richard42/ESP32FloppyTester/ESP32_FloppyTester/CodecGCR.cpp

//////////////////////////////////////////////////////////////////////////
// ESP32_FloppyTester
// CodecGCR.cpp
// 
// Copyright (C) 2024  Richard Goedeken
//
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
#include <stdint.h>
#include <stdlib.h>
#include <math.h>

#include <Arduino.h>

#include <map>

#include "FloppyTester.h"
#include "CodecGCR.h"

#define DELTA_ITEM(X) m_pusDeltaBuffers[(X)>>12][(X)&0x0fff]

//////////////////////////////////////////////////////////////////////////
// constructor and destructor

DecoderGCR::DecoderGCR(const uint16_t *pusDeltaBuffers[], uint32_t uiDeltaMax)
 : m_pusDeltaBuffers(pusDeltaBuffers)
 , m_uiDeltaMax(uiDeltaMax)
 , m_uiSectorDataLength(0)
{
}

DecoderGCR::~DecoderGCR()
{
}

//////////////////////////////////////////////////////////////////////////
// accessors

//////////////////////////////////////////////////////////////////////////
// static methods

bool DecoderGCR::DetectEncoding(const uint32_t auiCountByWavelen[16], const float afAverageByWavelen[16],
                                uint16_t *m_pusDeltaBuffers[], uint32_t uiDeltaMax, float fPeakCenters[3])
{
    // go through the histogram and find isolated peaks in the histogram
    uint32_t uiPeakIdx[4];
    uint32_t uiNumPeaks = 0;
    const uint32_t uiThreshold = uiDeltaMax / 30;
    const uint32_t uiLowThresh = uiDeltaMax / 250;
    bool bAboveThresh = false;
    for (uint32_t uiIdx = 0; uiIdx < 16; uiIdx++)
    {
        if (auiCountByWavelen[uiIdx] > uiThreshold)
        {
            if (bAboveThresh == false)
            {
                bAboveThresh = true;
                uiPeakIdx[uiNumPeaks] = uiIdx;
            }
            else
            {
                if (auiCountByWavelen[uiIdx] > auiCountByWavelen[uiPeakIdx[uiNumPeaks]])
                {
                    uiPeakIdx[uiNumPeaks] = uiIdx;
                }
            }
        }
        else
        {
            if (bAboveThresh == true)
            {
                bAboveThresh = false;
                uiNumPeaks++;
            }
        }
        if (uiNumPeaks == 4)
            break;
    }
    if (bAboveThresh == true)
        uiNumPeaks++;

    // special hack for test tracks written with all zeros -- they have a very small 3x signal
    if (uiNumPeaks == 2 && afAverageByWavelen[uiPeakIdx[0]] >= 3.0 && afAverageByWavelen[uiPeakIdx[0]] <= 4.2 &&
                           afAverageByWavelen[uiPeakIdx[1]] >= 6.1 && afAverageByWavelen[uiPeakIdx[1]] <= 8.2 &&
        (auiCountByWavelen[3] + auiCountByWavelen[4] + auiCountByWavelen[6] + auiCountByWavelen[7] + auiCountByWavelen[8]) > uiDeltaMax * 0.96)
    {
        uint32_t uiCount3x = 0, uiMaxIdx = 0;
        for (uint32_t ui = 9; ui <= 12; ui++)
        {
            const uint32_t uiThisCount = auiCountByWavelen[ui];
            uiCount3x += uiThisCount;
            if (ui == 9 || uiThisCount > auiCountByWavelen[uiMaxIdx])
            {
                uiMaxIdx = ui;
            }
        }
        if (uiCount3x > uiLowThresh)
        {
            uiPeakIdx[2] = uiMaxIdx;
            uiNumPeaks = 3;
        }
    }

    // and another special hack for test tracks written with all ones -- they have a small 2x signal
    if (uiNumPeaks == 2 && afAverageByWavelen[uiPeakIdx[0]] >= 3.0 && afAverageByWavelen[uiPeakIdx[0]] <= 4.2 &&
                           afAverageByWavelen[uiPeakIdx[1]] >= 9.2 && afAverageByWavelen[uiPeakIdx[1]] <= 12.2 &&
        (auiCountByWavelen[3] + auiCountByWavelen[4] + auiCountByWavelen[9] + auiCountByWavelen[10] + auiCountByWavelen[11] + auiCountByWavelen[12]) > uiDeltaMax * 0.94)
    {
        uint32_t uiCount2x = 0, uiMaxIdx = 0;
        for (uint32_t ui = 6; ui <= 8; ui++)
        {
            const uint32_t uiThisCount = auiCountByWavelen[ui];
            uiCount2x += uiThisCount;
            if (ui == 6 || uiThisCount > auiCountByWavelen[uiMaxIdx])
            {
                uiMaxIdx = ui;
            }
        }
        if (uiCount2x > uiLowThresh)
        {
            uiPeakIdx[2] = uiPeakIdx[1];
            uiPeakIdx[1] = uiMaxIdx;
            uiNumPeaks = 3;
        }
    }

    // if this track is GCR encoded, we expect to see 3 peaks, at 1x, 2x, and 3x of the base wavelength
    if (uiNumPeaks != 3)
        return false;

    fPeakCenters[0] = afAverageByWavelen[uiPeakIdx[0]];
    fPeakCenters[1] = afAverageByWavelen[uiPeakIdx[1]];
    fPeakCenters[2] = afAverageByWavelen[uiPeakIdx[2]];

    // use an iterative algorithm to converge on the true centers of each histogram peak
    for (uint32_t uiLoopIter = 0; uiLoopIter < 20; uiLoopIter++)
    {
        // calculate the average position of each delta value within +/- 0.5 microseconds of each peak
        float fNewPeakSums[3] = {0, 0, 0};
        uint32_t uiNewPeakCnts[3] = {0, 0, 0};
        for (uint32_t ui = 0; ui < uiDeltaMax; ui++)
        {
            uint32_t uiDelta = DELTA_ITEM(ui);
            if (uiDelta & 0x8000)
            {
                ui++;
                continue;
            }
            const float fWavelen = uiDelta / 80.0f;
            for (uint32_t uiPeak = 0; uiPeak < 3; uiPeak++)
            {
                if (fabsf(fWavelen - fPeakCenters[uiPeak]) <= 0.5f)
                {
                    fNewPeakSums[uiPeak] += fWavelen;
                    uiNewPeakCnts[uiPeak]++;
                }
            }
        }
        float fNewPeakCenters[3];
        for (uint32_t uiPeak = 0; uiPeak < 3; uiPeak++)
        {
            fNewPeakCenters[uiPeak] = fNewPeakSums[uiPeak] / uiNewPeakCnts[uiPeak];
        }
        // bail out if it has converged
        float fMaxPeakMove = 0.0f;
        for (uint32_t uiPeak = 0; uiPeak < 3; uiPeak++)
        {
            fMaxPeakMove = std::max(fMaxPeakMove, fabsf(fPeakCenters[uiPeak] - fNewPeakCenters[uiPeak]));
        }
        if (fMaxPeakMove < 0.0005)
        {
            //Serial.printf("GCR peak discovery converged after %i iterations.\r\n", uiLoopIter+1);
            break;
        }
        // fail if we have hit our iteration limit
        if (uiLoopIter == 19)
            return false;
        // otherwise, update our centers and try again
        for (uint32_t uiPeak = 0; uiPeak < 3; uiPeak++)
        {
            fPeakCenters[uiPeak] = fNewPeakCenters[uiPeak];
        }
    }

    // final duration spacing check
    //Serial.printf("GCR wavelength peaks at: %.3f, %.3f, %.3f\r\n", fPeakCenters[0], fPeakCenters[1], fPeakCenters[2]);
    if (fabsf(fPeakCenters[1] / fPeakCenters[0] - 2.0f) / 2.0f > 0.15)
        return false;
    if (fabsf(fPeakCenters[2] / fPeakCenters[0] - 3.0f) / 3.0f > 0.15)
        return false;

    // looks like it is GCR
    return true;
}

//////////////////////////////////////////////////////////////////////////
// modifiers

void DecoderGCR::DecodeTrack(geo_format_t eFormat, bool bDebugPrint, track_metadata_t& rsMeta, const float fPeakCenters[3])
{
    // clear sector counter
    rsMeta.ucSectorsFound = 0;

    // calculate thresholds
    const float fThresh[4] = { (3 * fPeakCenters[0] - fPeakCenters[1]) / 2,
                               (fPeakCenters[0] + fPeakCenters[1]) / 2,
                               (fPeakCenters[1] + fPeakCenters[2]) / 2,
                               (3 * fPeakCenters[2] - fPeakCenters[1]) / 2 };
    
    // iterate over all delta samples, looking for markers
    uint32_t uiFoundOnes = 0;
    for (uint32_t ui = 0; ui < m_uiDeltaMax; ui++)
    {
        // get binned time delta value and reset state if long delay is found
        uint32_t uiDelta = DELTA_ITEM(ui);
        if (uiDelta & 0x8000)
        {
            uiFoundOnes = 0;
            ui++;
            continue;
        }
        const float fWavelen = uiDelta / 80.0f;
        if (fWavelen < fThresh[0] || fWavelen > fThresh[3])
        {
            uiFoundOnes = 0;
            continue;
        }
        const uint32_t uiWavelen = (fWavelen < fThresh[1] ? 1 : (fWavelen < fThresh[2] ? 2 : 3));
        // handle state
        if (uiWavelen == 1)
        {
            uiFoundOnes++;
            continue;
        }
        if (uiFoundOnes < 10)
        {
            uiFoundOnes = 0;
            continue;
        }
        // we have found at least 10 ones (which is a sync pattern) and now a gap, indicating the start of a sector
        //if (bDebugPrint)
        //    Serial.printf("Found sync pattern with %i ones (sector start).\r\n", uiFoundOnes);
        
        ui = ReadSectorBytesC64(ui, fThresh, bDebugPrint, rsMeta);
        uiFoundOnes = 0;
    }

    if (bDebugPrint)
        Serial.printf("%i C64 sectors read.\r\n", rsMeta.ucSectorsFound);
}

//////////////////////////////////////////////////////////////////////////
// private methods

uint32_t DecoderGCR::ReadSectorBytesC64(uint32_t uiStartIdx, const float fThresh[4], bool bDebugPrint, track_metadata_t& rsMeta)
{
    const int8_t chDecodeGCR[32] = { -1, -1, -1, -1, -1, -1, -1, -1, -1, 8,  0,  1, -1, 12,  4,  5,
                                     -1, -1,  2,  3, -1, 15,  6,  7, -1, 9, 10, 11, -1, 13, 14, -1 };
    uint8_t ucBytes[512];
    uint8_t ucHeader[8];
    uint32_t uiBytesRead = 0;

    bool bWaitingForSync = false;
    bool bFoundHeader = false;
    bool bSectorAlreadyFound = false;
    uint32_t uiFoundOnes = 0;
    uint32_t uiPriorBits = 0;
    uint32_t uiNumPriorBits = 0;
    for (uint32_t ui = uiStartIdx; ui < m_uiDeltaMax; ui++)
    {
        // get binned time delta value and bail out if long delay is found
        uint32_t uiDelta = DELTA_ITEM(ui);
        if (uiDelta & 0x8000)
        {
            // error - long delay
            if (bDebugPrint)
                Serial.printf("[Sector read error: long delay]\r\n");
            return ui + 2;
        }
        const float fWavelen = uiDelta / 80.0f;
        if (fWavelen < fThresh[0] || fWavelen > fThresh[3])
        {
            if (bWaitingForSync)
            {
                uiFoundOnes = 0;
                continue;
            }
            // error - invalid duration
            if (bDebugPrint)
                Serial.printf("[Sector read error: invalid duration %.3fus with uiBytesRead=%i]\r\n", fWavelen, uiBytesRead);
            return ui + 2;
        }
        const uint32_t uiWavelen = (fWavelen < fThresh[1] ? 1 : (fWavelen < fThresh[2] ? 2 : 3));
        // handle sync pattern between header and data
        if (bWaitingForSync)
        {
            if (uiWavelen == 1)
            {
                uiFoundOnes++;
                continue;
            }
            if (uiFoundOnes < 10)
            {
                uiFoundOnes = 0;
                continue;
            }
            bWaitingForSync = false;
            uiPriorBits = 1;
            uiNumPriorBits = uiWavelen;
            continue;
        }
        // accumulate bits
        uiPriorBits = (uiPriorBits << uiWavelen) + 1;
        uiNumPriorBits += uiWavelen;
        if (uiNumPriorBits < 10)
            continue;
        // write out one byte
        const uint32_t uiGCRWord = (uiPriorBits >> (uiNumPriorBits - 10));
        uiNumPriorBits -= 10;
        if (uiNumPriorBits == 0)
            uiPriorBits = 0;
        else
            uiPriorBits &= (1 << uiNumPriorBits) - 1;
        const char chHighNybble = chDecodeGCR[uiGCRWord >> 5];
        const char chLowNybble = chDecodeGCR[uiGCRWord & 31];
        if (chHighNybble == -1)
        {
            if (bDebugPrint)
                Serial.printf("[Sector read error: illegal GCR pattern 0x%02x]\r\n", uiGCRWord >> 5);
            return ui + 1;
        }
        if (chLowNybble == -1)
        {
            if (bDebugPrint)
                Serial.printf("[Sector read error: illegal GCR pattern 0x%02x]\r\n", uiGCRWord & 31);
            return ui + 1;
        }
        const uint8_t ucNewByte = (chHighNybble << 4) + chLowNybble;
        ucBytes[uiBytesRead++] = ucNewByte;
        // handle first byte (block ID)
        if (uiBytesRead == 1)
        {
            if (ucNewByte != 7 && ucNewByte != 8)
            {
                if (bDebugPrint)
                    Serial.printf("[Sector read error: illegal block ID 0x%02x]\r\n", ucNewByte);
                return ui + 1;
            }
            if (ucNewByte == 7 && !bFoundHeader)
            {
                // we found the data block but no header block, so just bail out
                return ui + 1;
            }
        }
        // handle completion of header block
        if (uiBytesRead == 8 && ucBytes[0] == 8)
        {
            // copy it to separate header array and wait for another sync pattern
            bFoundHeader = true;
            memcpy(ucHeader, ucBytes, 8);
            uiBytesRead = 0;
            bWaitingForSync = true;
            uiFoundOnes = 0;
            uiPriorBits = 0;
            uiNumPriorBits = 0;
            // Sector ID record
            const bool bChecksumGood = (ucHeader[1] == (ucHeader[2] ^ ucHeader[3] ^ ucHeader[4] ^ ucHeader[5]));
            if (bDebugPrint)
                Serial.printf("Sector ID: Track %i, Sector %i, Format ID=%02x%02x Checksum=%02x (%s)\r\n", ucHeader[3], ucHeader[2] + 1, ucHeader[4],
                              ucHeader[5], ucHeader[1], (bChecksumGood ? "GOOD" : "BAD"));
            // set metadata
            if (rsMeta.ucSectorsFound < 21)
            {
                for (uint32_t ui = 0; ui < rsMeta.ucSectorsFound; ui++)
                {
                    if (rsMeta.ucSectorNum[ui] == ucHeader[2] + 1 && rsMeta.ucSectorGoodID[ui] && rsMeta.ucSectorGoodData[ui])
                        bSectorAlreadyFound = true;
                }
                if (!bSectorAlreadyFound)
                {
                    // C64 tracks are numbered from one and sectors are numbered from zero
                    // but in our track_metadata_t structure, sector numbers are expected to be starting
                    // from one, while cylinders start at zero
                    rsMeta.ucSectorNum[rsMeta.ucSectorsFound] = ucHeader[2] + 1;
                    rsMeta.ucSectorSide[rsMeta.ucSectorsFound] = 0;
                    rsMeta.ucSectorCylinder[rsMeta.ucSectorsFound] = ucHeader[3] - 1;
                    rsMeta.ucSectorGoodID[rsMeta.ucSectorsFound] = (bChecksumGood ? 1 : 0);
                }
            }
            continue;
        }
        // handle completion of data block
        if (uiBytesRead == 258 && ucBytes[0] == 7)
        {
            // Sector data
            uint8_t ucDataChecksum = 0;
            for (uint32_t ui = 1; ui <= 0x100; ui++)
            {
                ucDataChecksum ^= ucBytes[ui];
            }
            const bool bDataChecksumGood = (ucBytes[0x101] == ucDataChecksum);
            if (bDebugPrint)
                Serial.printf("Sector data: 256 bytes with Checksum=%s\r\n", (bDataChecksumGood ? "GOOD" : "BAD"));
            // set metadata
            if (rsMeta.ucSectorsFound < 21 && !bSectorAlreadyFound)
            {
                // if the sector was previously read (but header or data checksum failed) then
                // overwrite the old results with the new ones
                int32_t iSectorPreviousBadRead = -1;
                for (uint32_t ui = 0; ui < rsMeta.ucSectorsFound; ui++)
                {
                    // we only need to check for the existence of the same sector that we're reading now,
                    // because if it was previously read then it must have failed, otherwise bSectorAlreadyFound would
                    // be true and we wouldn't be executing this code.
                    if (rsMeta.ucSectorNum[ui] == rsMeta.ucSectorNum[rsMeta.ucSectorsFound])
                        iSectorPreviousBadRead = ui;
                }
                if (iSectorPreviousBadRead >= 0)
                {
                    rsMeta.ucSectorSide[iSectorPreviousBadRead] = rsMeta.ucSectorSide[rsMeta.ucSectorsFound];
                    rsMeta.ucSectorCylinder[iSectorPreviousBadRead] = rsMeta.ucSectorCylinder[rsMeta.ucSectorsFound];
                    rsMeta.ucSectorGoodID[iSectorPreviousBadRead] = rsMeta.ucSectorGoodID[rsMeta.ucSectorsFound];
                    rsMeta.ucSectorGoodData[iSectorPreviousBadRead] = (bDataChecksumGood ? 1 : 0);
                    rsMeta.uiSectorDataCRC[iSectorPreviousBadRead] = ucDataChecksum;
                }
                else
                {
                    rsMeta.ucSectorGoodData[rsMeta.ucSectorsFound] = (bDataChecksumGood ? 1 : 0);
                    rsMeta.uiSectorDataCRC[rsMeta.ucSectorsFound] = ucDataChecksum;
                    rsMeta.ucSectorsFound++;
                }
            }
            return ui + 1;
        }
    }
}

//////////////////////////////////////////////////////////////////////////
// constructor/destructor for encoding class

EncoderGCR::EncoderGCR(uint16_t *pusDeltaBuffers[], geo_format_t eFormat, int iSides, int iTracks, int iSectors)
 : EncoderBase(pusDeltaBuffers, eFormat, iSides, iTracks, iSectors)
 , m_uiBaseTime(0)
 , m_uiZeroes(0)
{
}

EncoderGCR::~EncoderGCR()
{
}

//////////////////////////////////////////////////////////////////////////
// modifiers for encoding class

uint32_t EncoderGCR::EncodeTrack(encoding_pattern_t ePattern, int iDriveTrack, int iDriveSide)
{
    if (m_eGeoFormat == FMT_C64)
    {
        // "iDriveTrack + 1" because cylinders are numbered from zero, but C64 "Track" numbers are numbered from one
        return EncodeTrack180kC64(ePattern, iDriveTrack + 1, iDriveSide);
    }
}

uint32_t EncoderGCR::EncodeTrack180kC64(encoding_pattern_t ePattern, int iDriveTrack, int iDriveSide)
{
    // 200ms / 4us = 50,000 bits / 8 = 6250 bytes per track

    // calculate base timing duration and sector count for this track
    const uint32_t uiNumSectors = (iDriveTrack < 18 ? 21 : (iDriveTrack < 25 ? 19 : (iDriveTrack < 31 ? 18 : 17)));
    const float fBaseTime = (iDriveTrack < 18 ? 3.25f : (iDriveTrack < 25 ? 3.5f : (iDriveTrack < 31 ? 3.75f : 4.0f)));
    m_uiBaseTime = (uint32_t) (fBaseTime * 80);
    const uint32_t uiSectorGapBytes = (iDriveTrack < 18 ? 8 : (iDriveTrack < 25 ? 15 : (iDriveTrack < 31 ? 11 : 9)));

    const uint8_t ucFormatID[2] = { '0', '0' };

    // start with one millisecond of sync bits so that at the end of the track we will overwrite this sync lead-in
    // and not leave an unused bit of sector header/data in between end and start of the track
    for (uint32_t ui = 0; ui < (uint32_t) (1000 / fBaseTime); ui++)
    {
        DELTA_ITEM(m_uiDeltaPos) = m_uiBaseTime;
        m_uiDeltaPos++;
    }
    
    // write each sector
    for (uint32_t uiSector = 0; uiSector < uiNumSectors; uiSector++)
    {
        uint8_t ucSectorData[256];
        calc_sector_data(ePattern, 256, uiSector, ucSectorData);

        // Header sync pattern (40 one bits)
        for (uint32_t ui = 0; ui < 40; ui++)
        {
            DELTA_ITEM(m_uiDeltaPos) = m_uiBaseTime;
            m_uiDeltaPos++;
        }
        
        // Header
        WriteByte(0x08);
        WriteByte(uiSector ^ iDriveTrack ^ ucFormatID[0] ^ ucFormatID[1]);
        WriteByte(uiSector);
        WriteByte(iDriveTrack);
        WriteByte(ucFormatID[0]);
        WriteByte(ucFormatID[1]);
        WriteByte(0x0f);
        WriteByte(0x0f);

        // Header gap
        for (uint32_t ui = 0; ui < 9; ui++)
        {
            WriteByte(0x55);
        }

        // Data sync pattern (40 one bits)
        for (uint32_t ui = 0; ui < 40; ui++)
        {
            DELTA_ITEM(m_uiDeltaPos) = m_uiBaseTime;
            m_uiDeltaPos++;
        }

        // Data block
        WriteByte(0x07);
        uint8_t ucChecksum = 0;
        for (uint32_t uiDataIdx = 0; uiDataIdx < 256; uiDataIdx++)
        {
            ucChecksum ^= ucSectorData[uiDataIdx];
            WriteByte(ucSectorData[uiDataIdx]);
        }
        WriteByte(ucChecksum);
        WriteByte(0x00);
        WriteByte(0x00);
        
        // inter-sector gap
        for (uint32_t ui = 0; ui < uiSectorGapBytes; ui++)
        {
            WriteByte(0x55);
        }
    }

    return m_uiDeltaPos;
}

//////////////////////////////////////////////////////////////////////////
// private helper methods

void EncoderGCR::WriteBit(int iBit)
{
    if (iBit)
    {
        DELTA_ITEM(m_uiDeltaPos) = m_uiBaseTime * (m_uiZeroes + 1);
        m_uiDeltaPos++;
        m_uiZeroes = 0;
    }
    else
    {
        m_uiZeroes++;
    }
    return;
}

void EncoderGCR::WriteNybble(int iNybble)
{
    static const uint8_t ucQuintuples[16] = { 10, 11, 18, 19, 14, 15, 22, 23, 9, 25, 26, 27, 13, 29, 30, 21 };
    uint8_t ucQuint = ucQuintuples[iNybble & 15];
    for (uint32_t ui = 0; ui < 5; ui++)
    {
        WriteBit(ucQuint & 16);
        ucQuint <<= 1;
    }
}

void EncoderGCR::WriteByte(int iByte)
{
    WriteNybble((iByte >> 4) & 15);
    WriteNybble(iByte & 15);
}

void EncoderGCR::calc_sector_data(encoding_pattern_t ePattern, uint32_t uiLength, uint32_t uiSectorNum, uint8_t *pucSectorData)
{
    // seed PRNG if necessary
    if (m_eGeoFormat == ENC_RANDOM)
    {
        uint32_t uiCurCycles;
        asm volatile("  rsr %0, ccount                \n"
                     : "=a"(uiCurCycles) );
        srand(uiCurCycles);
    }

    // write bytes
    for (uint32_t uiByteIdx = 0; uiByteIdx < uiLength; uiByteIdx++)
    {
        switch(ePattern)
        {
            case ENC_ZEROS:
                pucSectorData[uiByteIdx] = 0xEE;
                break;
            case ENC_ONES:
                pucSectorData[uiByteIdx] = 0xE5;
                break;
            case ENC_SIXES:
                pucSectorData[uiByteIdx] = 0x0F;
                break;
            case ENC_EIGHTS:
                pucSectorData[uiByteIdx] = 0x28;
                break;
            case ENC_RANDOM:
                pucSectorData[uiByteIdx] = (rand() & 0xff);
                break;
        }
    }
}
